desertkun/pods/datasheets/nRF24L01+.jpg

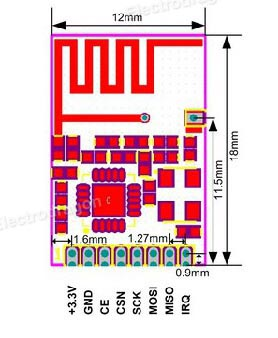
datasheets/nRF24L01+.jpg
