desertkun/pods/datasheets/sh1106.jpg

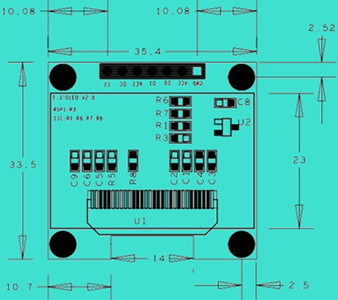
datasheets/sh1106.jpg
