desertkun/pods/datasheets/SWD.png

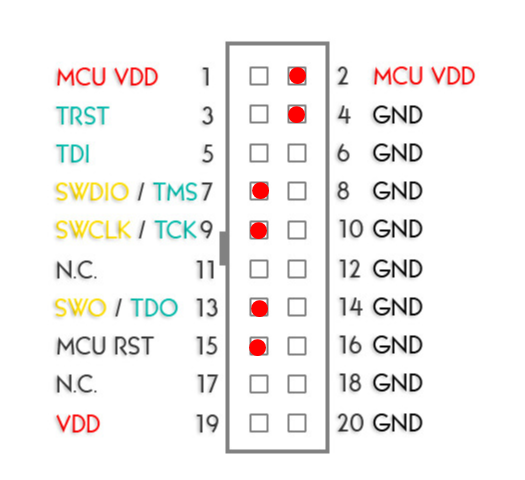
datasheets/SWD.png
