desertkun/pods/datasheets/tp4056.jpg

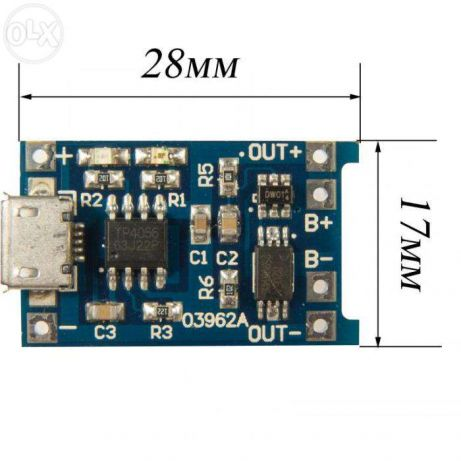
datasheets/tp4056.jpg
