desertkun/pods/src/app/melodies.cpp

#include "app/melodies.h"

// Melody Data
// ----------------------------------------------------------------------------
// The melody is stored as an array of 16 bit unsigned integers (uint16_t)
// where each integer encodes the note, octave and duration
//
//   [duration][octave][note]  - ddddddddoooonnnn
//
//   note (nnnn) is 4 bits which are the note to play
//    C = 0, C# = 1, D = 2, D# = 3, E = 4, F = 5,
//    F# = 6, G = 7, G# = 8, A = 9, A# = 10, B = 11,
//    SILENT = 15
//
//   octave (oooo) is 4 bits which indicate the octave to play that note in,
//   maximum octave we can handle is 8, minimum is 0
//    octave 0 = 0 .. octave 8 = 8
//
//   duration (dddddddd) is the duration of the note to play in units of tempo
//    hold note for 10 tempos = 10
//
// You can use the following web page to create the Melody data for you:
//    http://sparks.gogo.co.nz/midi_tone.html
//
// You can also select a human readable/editable output format on that page
// instead of this short form version.

const uint16_t Melodies::Intro[] = {
	0b0111100000110101, 0b0111100000110111, 0b1111000000111010, 0b1111111100110111,
	0b1111111100110111, 0b1111111100110111, 0b1100001100110111, 0b1111000011111111,
	0b0111100000110101, 0b0111100000110111, 0b1111000000111010, 0b1111000001000101,
	0b1111111101000011, 0b1111111101000011, 0b1101001001000011, 0b1111000001000010,
	0b1111111101000000, 0b1111111101000000, 0b1101001001000000, 0b1111000000111010,
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
	0b0001011100001000, 0b0000101101100001, 0b0000111011111111, 0b0001001110011011,
	0b0001101011111111, 0b0001101010000000, 0b0001011011111111, 0b0001111101010001,
	0b0000111011111111, 0b0001111000011010, 0,
};

const uint16_t Melodies::PlaceBomb[] = {
	0b0011100000000111, 0,
};
