desertkun/pods/inc/app/gs/game.h

/*
 * game.h
 *
 *  Created on: Mar 11, 2018
 *      Author: desertkun
 */

#ifndef APP_GS_GAME_H_
#define APP_GS_GAME_H_

#include "gamestate.h"
#include "app/messages.h"

#define MAP_WIDTH 16
#define MAP_HEIGHT 7

#define MAP_OFFSET_X 0
#define MAP_OFFSET_Y 8

#define MAX_BOMBS 5

namespace gs
{

enum class Tile
{
	empty = 0,
	wall,
	block,
	blockWithPowerup,
	blockWithExtraBomb,
	powerup,
	extraBomb,
	explosion
};

class Game;

enum class PlayerState
{
	normal = 0,
	moving = 1
};

enum class BombState
{
	normal,
	active,
	explosion
};

struct Bomb
{
	static const uint32_t TIME, EXPLOSION_TIME;

	BombState state;
	uint32_t timer;
	bool _render;
	uint8_t x, y;
	uint8_t power;

	void removeExplosions();
	void explode();
	void place(uint8_t x, uint8_t y, uint8_t power);
	void update(uint32_t dt);
	void render();
};

struct Player
{
	Bomb bombs[MAX_BOMBS];
	PlayerState state;
	uint8_t x, y, targetX, targetY, movingTimer, movedBy;
	int8_t offsetX, offsetY;
	uint8_t bombPower, bombCount;
	const unsigned char* sprite;

	void init(uint8_t x, uint8_t y, const unsigned char* sprite);
	void update(uint32_t dt);
	void moveTo(uint8_t x, uint8_t y);
	void render();
	void moved();
};

class Game: public GameState
{
public:
	static Game s_instance;

public:
	static Game* switchTo();

public:
	virtual ID getID() const override { return ID::search; }
	virtual void update(uint32_t dt) override;
	virtual void release() override;
	virtual void init() override;
	virtual void messageReceived(uint8_t messageType, uint8_t dataSize, void* data) override;

public:
	static void SetDirty() { Game::s_instance.m_dirty = true; }

	void serialize(msg::Map* mapMsg);
	void deserialize(msg::Map* mapMsg);
	void started();

	bool checkTile(uint8_t x, uint8_t y);

	void addPowerUp() { m_activePowerUps++; }
	void removePowerUp() { m_activePowerUps--; }
	void addShake() { m_activeShake++; }
	void removeShake() { m_activeShake--; }


	void setTile(uint8_t x, uint8_t y, Tile tile);
	Tile getTile(uint8_t x, uint8_t y) const;

private:
	bool checkLocation(uint8_t x, uint8_t y) const;
	void sendMyPosition();
	void clearCell(uint8_t x, uint8_t y);
	void renderCell(uint8_t x, uint8_t y, const unsigned char* image);
	void getReady();
	void render();
	void generate();
	void build();
	void disconnect();

	const Player& getMyPlayer() const { return m_players[m_myPlayerId]; }
	const Player& getOtherPlayer() const { return m_players[1 - m_myPlayerId]; }

	Player& getMyPlayer() { return m_players[m_myPlayerId]; }
	Player& getOtherPlayer() { return m_players[1 - m_myPlayerId]; }

private:
	Tile m_tiles[MAP_WIDTH * MAP_HEIGHT];
	Player m_players[2];
	uint8_t m_myPlayerId;
	uint32_t m_seed;
	uint8_t m_activePowerUps, m_activeShake;

	uint32_t m_refreshTimer;
	bool m_dirty;

	msg::Move m_moveMsg;
	bool m_gotMoveMsg;

	msg::Bomb m_bombMsg;
	bool m_gotBombMsg;

	msg::Result m_resultMsg;
	bool m_gotResultMsg;
};

};


#endif /* APP_GS_GAME_H_ */
